peng-zhihui/HDMI-PI/2.Firmware/2.东芝方案/HDMI/Extra/panel.h

#ifndef _PANEL
#define _PANEL

#include "main.h"

const uint8_t panel_init_data1[]={
0xFF,0x01,
0xFB,0x01,
0xFF,0x02,
0xFB,0x01,
0xFF,0x03,
0xFB,0x01,
0xFF,0x04,
0xFB,0x01,
0xFF,0x05,
0xFB,0x01,
0xD7,0x31,
0xD8,0x7E};

const uint8_t panel_init_data2[]={
0xFF,0x00,
0xFB,0x01,
0xBA,0x03,
0x36,0x00,
0xB0,0x00,
0xD3,0x08,
0xD4,0x0E,
0xD5,0x0F,
0xD6,0x48,
0xD7,0x00,
0xD9,0x00,
0xFB,0x01,
0xFF,0xEE,
0x40,0x00,
0x41,0x00,
0x42,0x00,
0xFB,0x01,
0xFF,0x01,
0xFB,0x01,
0x01,0x55,
0x04,0x0C,
0x05,0x3A,
0x06,0x50,
0x07,0xD0,
0x0A,0x0F,
0x0C,0x06,
0x0D,0x7F,
0x0E,0x7F,
0x0F,0x70,
0x10,0x63,
0x11,0x3C,
0x12,0x5C,
0x13,0x5A,
0x14,0x5A,
0x15,0x60,
0x16,0x15,
0x17,0x15,
0x23,0x00,
0x24,0x00,
0x25,0x00,
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
};

#endif
